rkchwsk/Backpack-for-any-box/stl/BP v65_BP v65_left back_3_right back midplate.stl

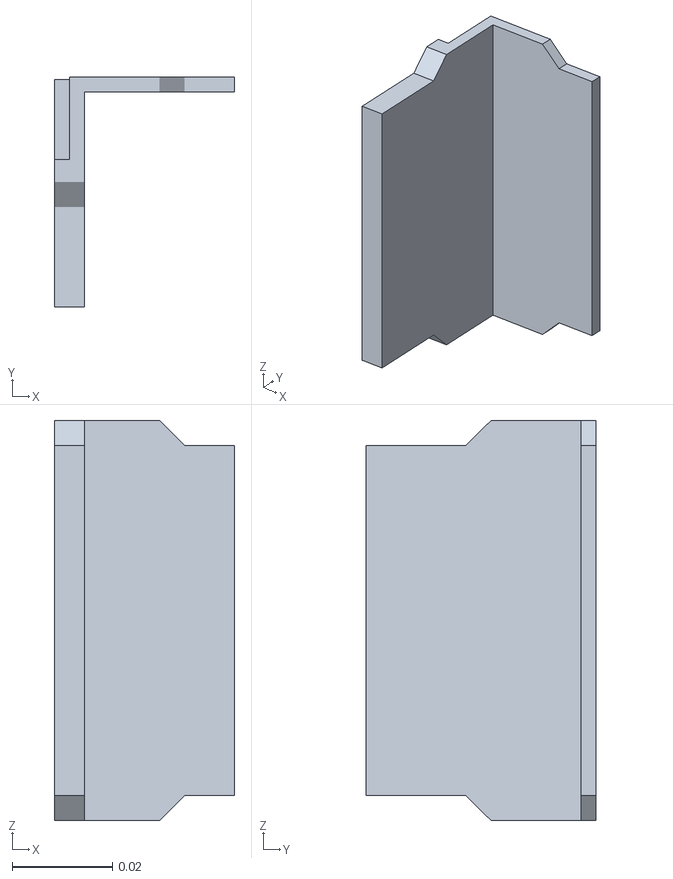
[picture p16: CAD file, 2023-12-04]
stl/BP v65_BP v65_left back_3_right back midplate.stl
0.036 x 0.046 x 0.08
