rkchwsk/Backpack-for-any-box/stl/BP v65_BP v65_right front_1_Ratchet_1_pin_1_pin.stl

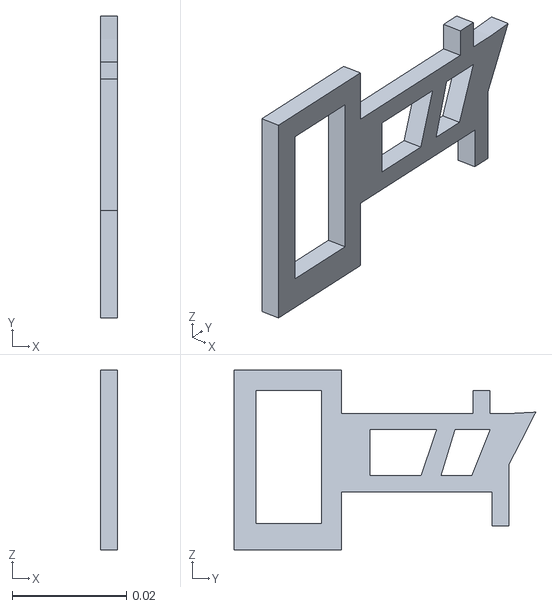
[picture p17: CAD file, 2023-12-04]
stl/BP v65_BP v65_right front_1_Ratchet_1_pin_1_pin.stl
0.003 x 0.0528 x 0.0315
