rkchwsk/Backpack-for-any-box/stl/BP v65_BP v65_Left front (right Mirror)_1_90 angle flat short (1)(Mirror)_1_90 angle flat short.stl

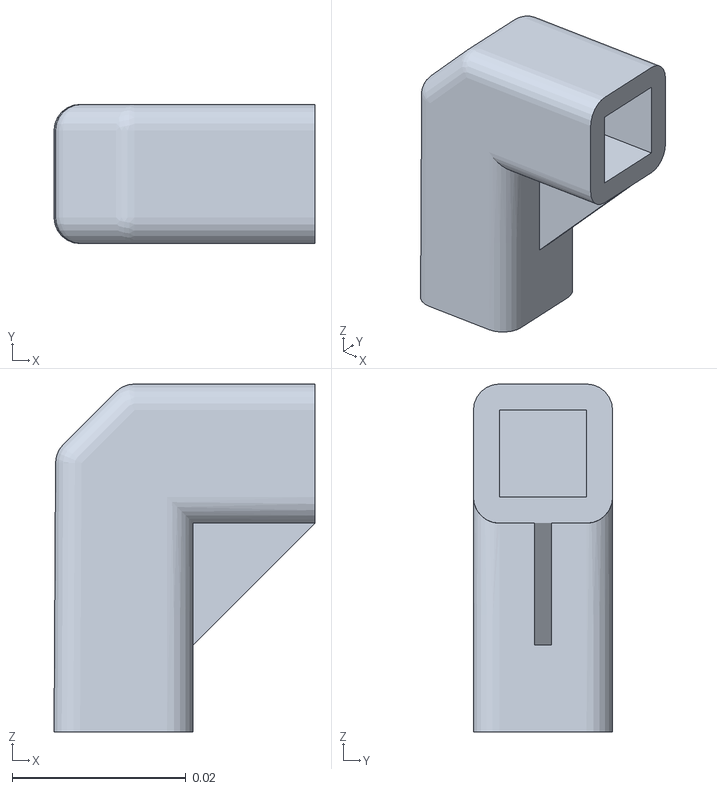
[picture p18: CAD file, 2023-12-04]
stl/BP v65_BP v65_Left front (right Mirror)_1_90 angle flat short (1)(Mirror)_1_90 angle flat short.stl
0.03 x 0.016 x 0.04
