rkchwsk/Backpack-for-any-box/stl/BP v65_BP v65_Back_1_internal rails_1_internal rail 1.stl

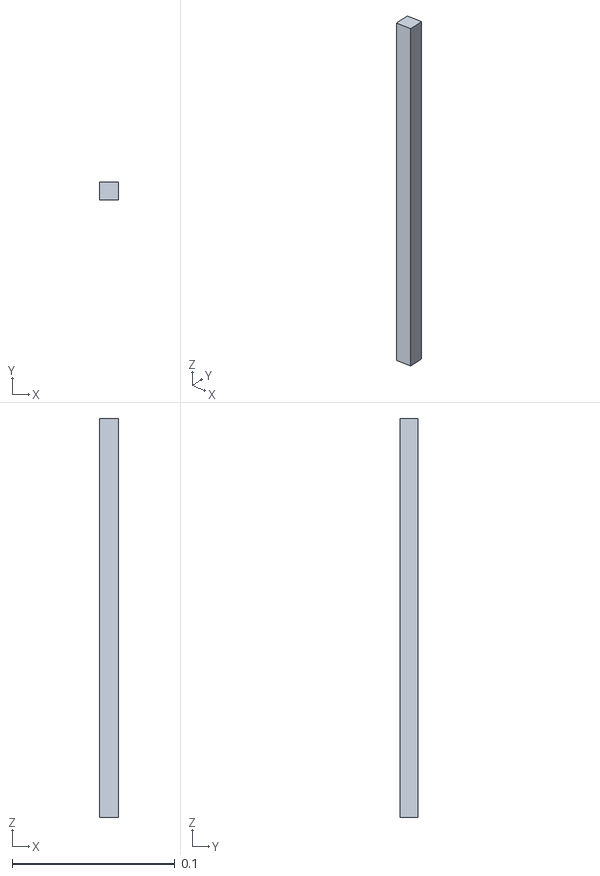
[picture p19: CAD file, 2023-12-04]
stl/BP v65_BP v65_Back_1_internal rails_1_internal rail 1.stl
0.0115 x 0.0112 x 0.245
