rkchwsk/Backpack-for-any-box/stl/BP v65_BP v65_right front_1_Ratchet_1_pin cover_1_pin cover.stl

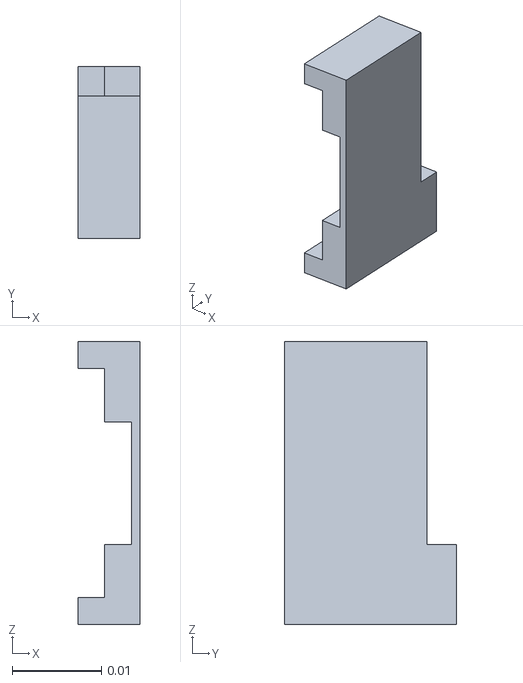
[picture p20: CAD file, 2023-12-04]
stl/BP v65_BP v65_right front_1_Ratchet_1_pin cover_1_pin cover.stl
0.007 x 0.0193 x 0.0317
