rkchwsk/Backpack-for-any-box/stl/BP v65_BP v65_Back_1_internal rails_1_Bottom rails hinge_1_Bottom rails hinge moving.stl

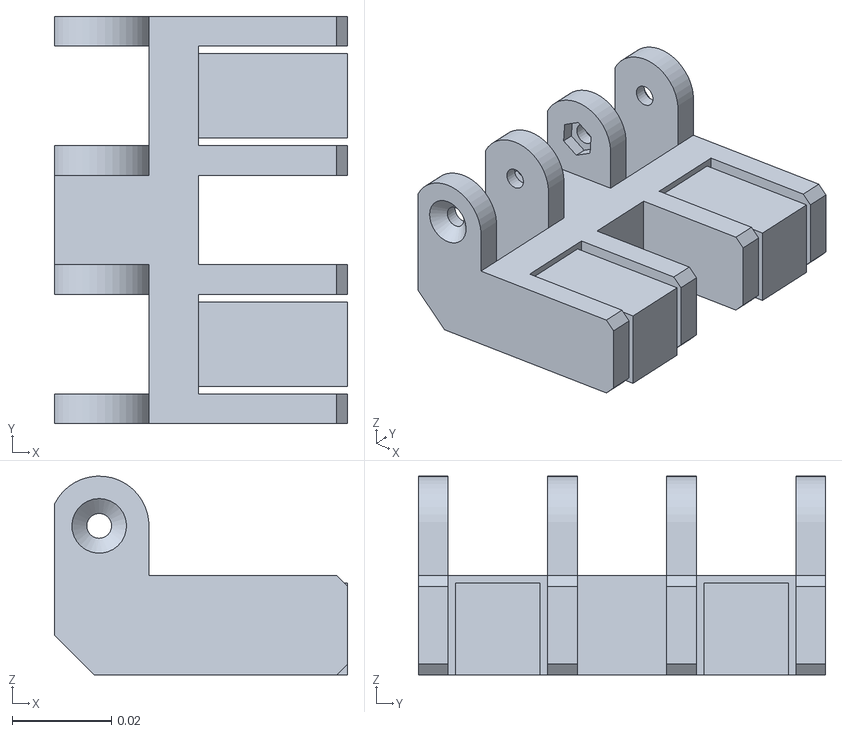
[picture p21: CAD file, 2023-12-04]
stl/BP v65_BP v65_Back_1_internal rails_1_Bottom rails hinge_1_Bottom rails hinge moving.stl
0.059 x 0.082 x 0.04
