rkchwsk/Backpack-for-any-box/stl/BP v65_BP v65_Back_1_internal rails_1_locker_1_Locker.stl

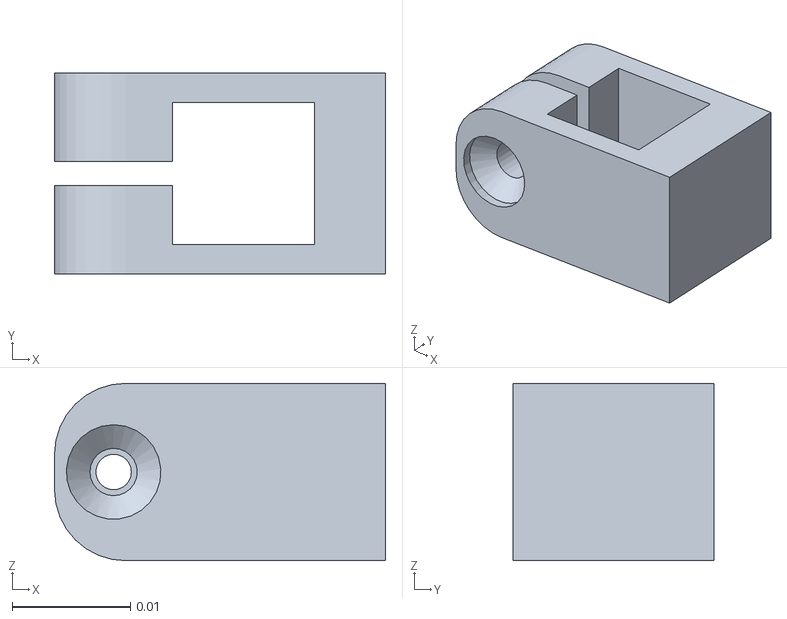
[picture p22: CAD file, 2023-12-04]
stl/BP v65_BP v65_Back_1_internal rails_1_locker_1_Locker.stl
0.028 x 0.017 x 0.015
