rkchwsk/Backpack-for-any-box/stl/BP v65_BP v65_right front_1_Ratchet_1_Rope locker_1_Rope locker.stl

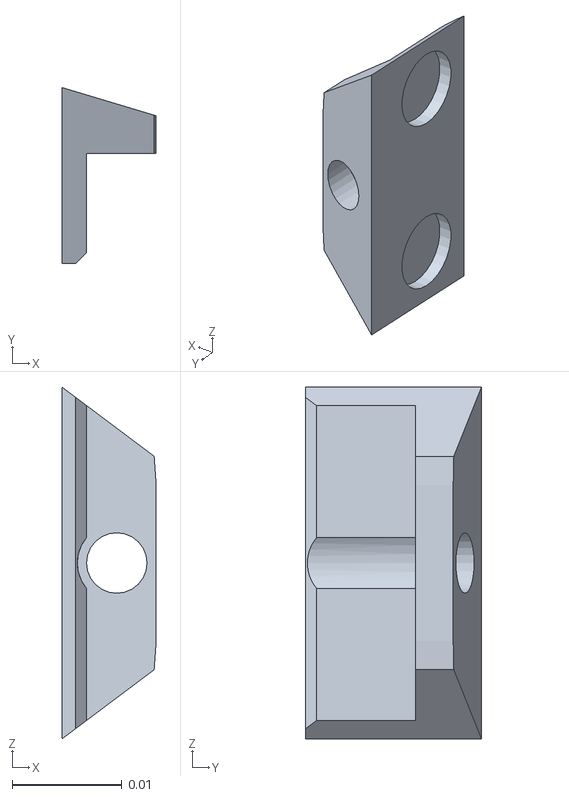
[picture p23: CAD file, 2023-12-04]
stl/BP v65_BP v65_right front_1_Ratchet_1_Rope locker_1_Rope locker.stl
0.00859 x 0.016 x 0.032
