rkchwsk/Backpack-for-any-box/stl/BP v65_BP v65_Left front (right Mirror)_1_rope guide straigt (1)(Mirror)_1_rope guide straigt.stl

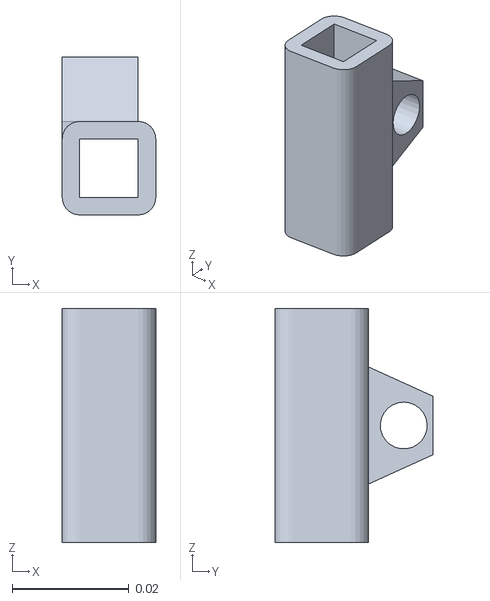
[picture p24: CAD file, 2023-12-04]
stl/BP v65_BP v65_Left front (right Mirror)_1_rope guide straigt (1)(Mirror)_1_rope guide straigt.stl
0.016 x 0.027 x 0.04
