rkchwsk/Backpack-for-any-box/stl/BP v65_BP v65_Back_1_internal rails_1_internal rail 2.stl

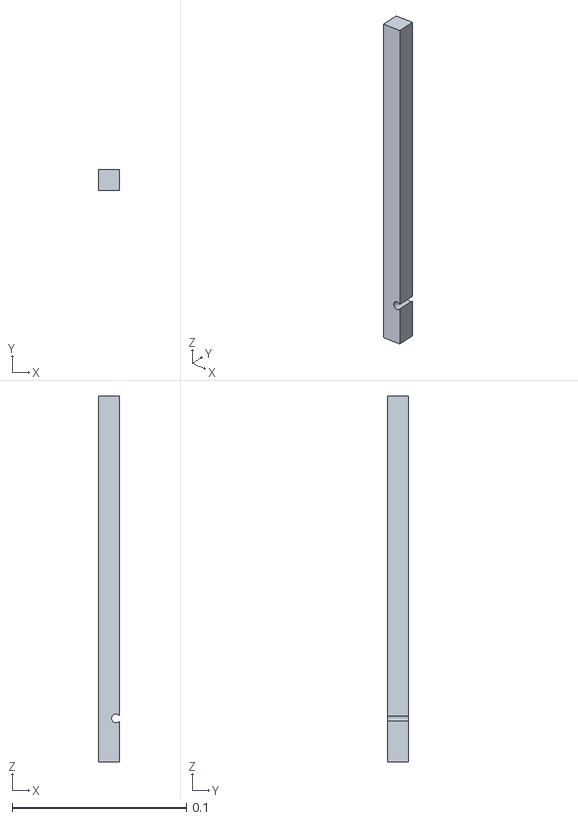
[picture p25: CAD file, 2023-12-04]
stl/BP v65_BP v65_Back_1_internal rails_1_internal rail 2.stl
0.012 x 0.012 x 0.21
