rkchwsk/Backpack-for-any-box/stl/BP v65_BP v65_right front_1_Ratchet_1_Bobbin_1_bobbin bottom.stl

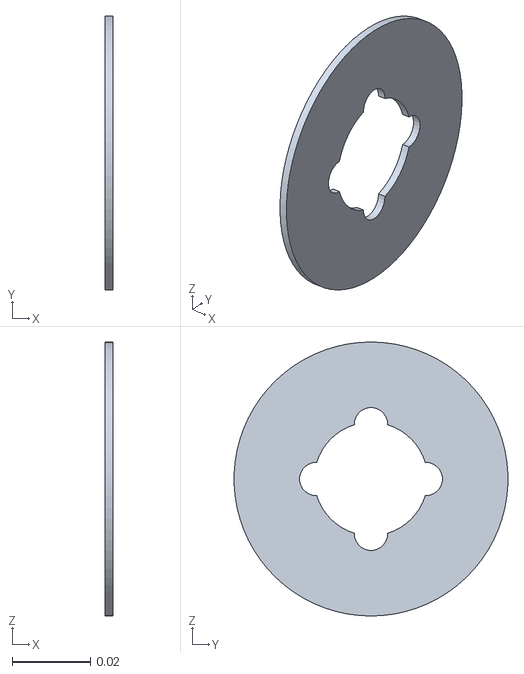
[picture p26: CAD file, 2023-12-04]
stl/BP v65_BP v65_right front_1_Ratchet_1_Bobbin_1_bobbin bottom.stl
0.002 x 0.0699 x 0.07
