rkchwsk/Backpack-for-any-box/stl/BP v65_BP v65_Back_1_internal rails_1_Bottom rails hinge_1_Bottom rails hinge stationary 1.stl

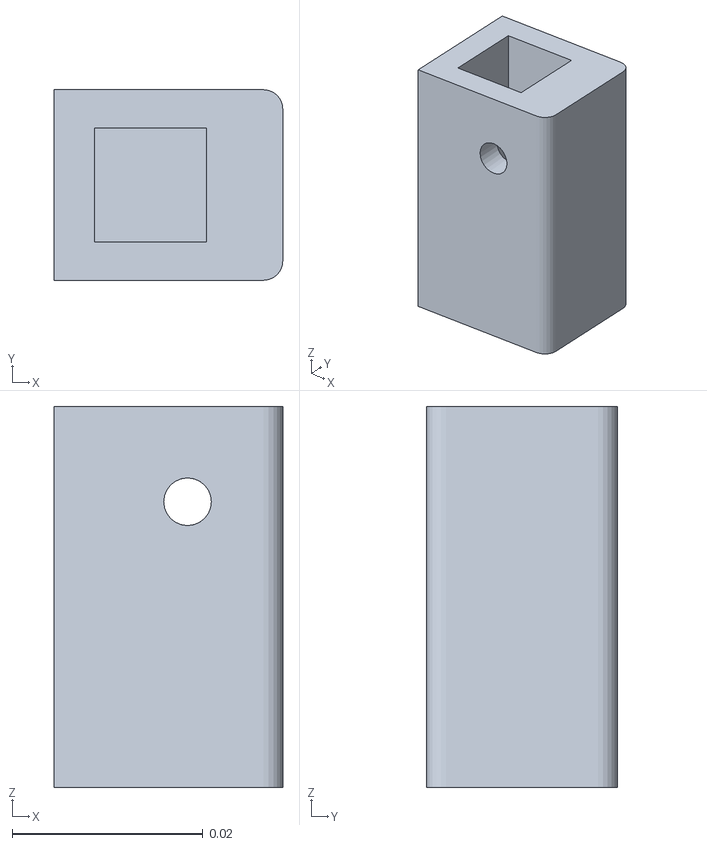
[picture p27: CAD file, 2023-12-04]
stl/BP v65_BP v65_Back_1_internal rails_1_Bottom rails hinge_1_Bottom rails hinge stationary 1.stl
0.024 x 0.02 x 0.04
