rkchwsk/Backpack-for-any-box/stl/BP v65.stl

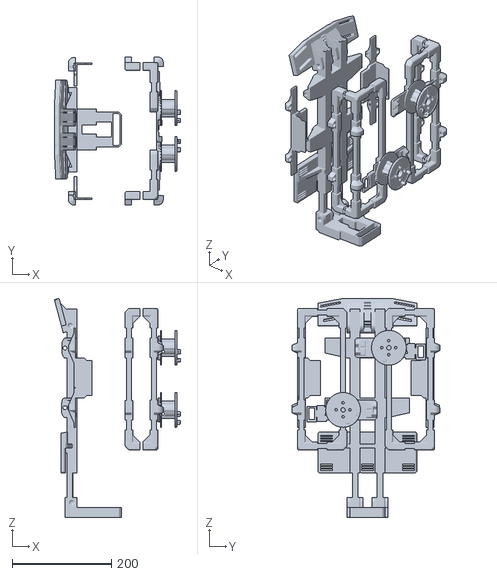
[picture p28: CAD file, 2023-12-04]
stl/BP v65.stl
254.2 x 298.2 x 440.7
