rkchwsk/Backpack-for-any-box/stl/BP v65_BP v65_Back_1_Back middle bottom_1_Back middle bottom.stl

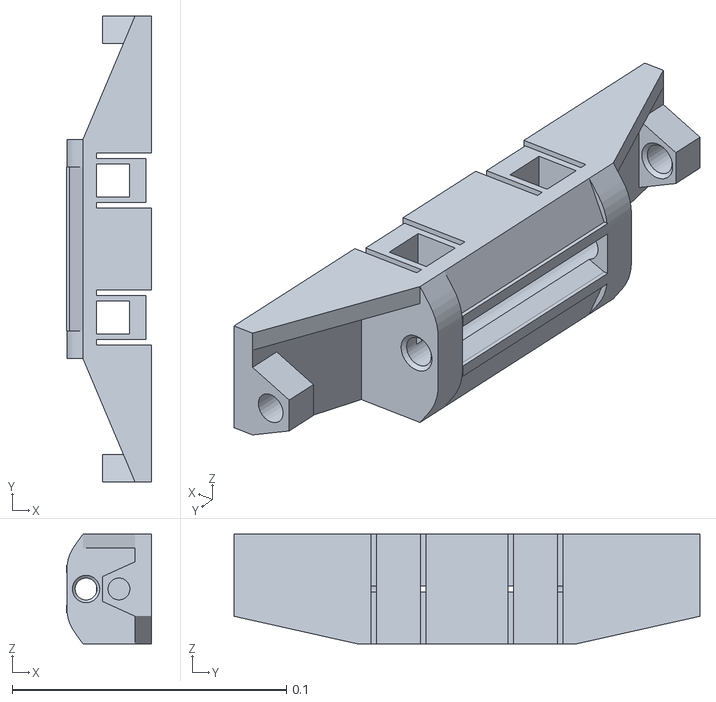
[picture p29: CAD file, 2023-12-04]
stl/BP v65_BP v65_Back_1_Back middle bottom_1_Back middle bottom.stl
0.031 x 0.17 x 0.04
